iwandwip/TemperatureControlLab/sketch/py/data/test_Heaters.png

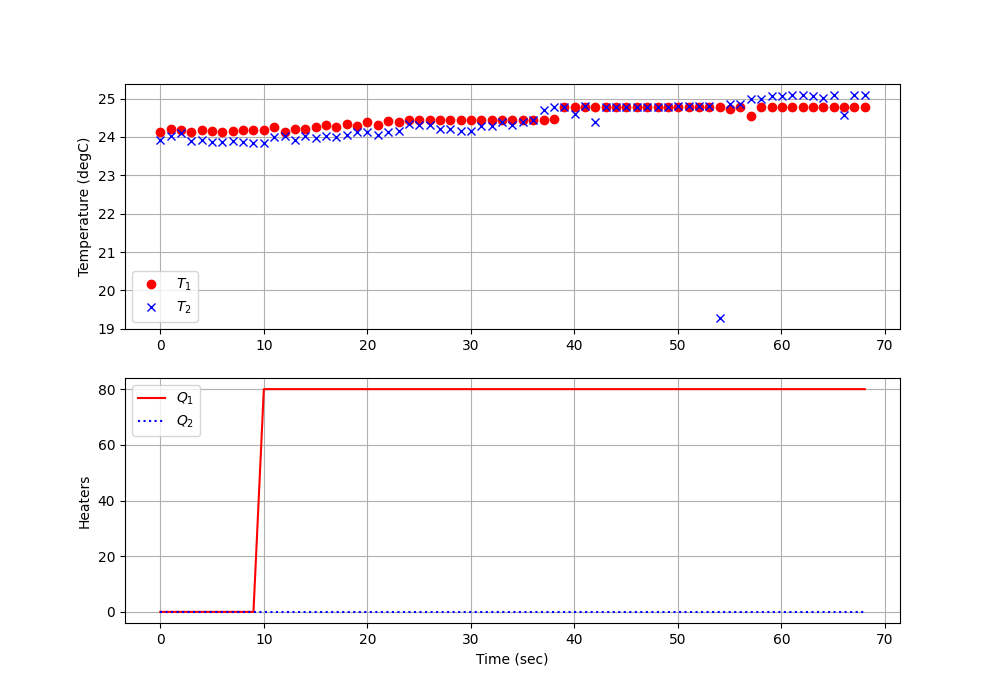
sketch/py/data/test_Heaters.png
