iwandwip/TemperatureControlLab/sketch/py/data/test_Models.png

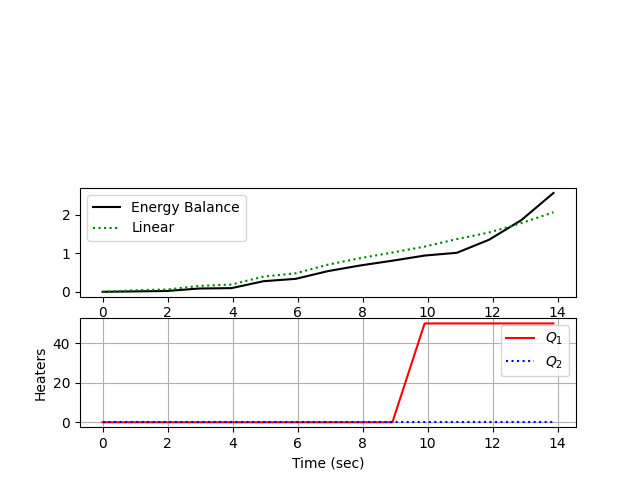
sketch/py/data/test_Models.png
