iwandwip/TemperatureControlLab/sketch/py/data/test_PID.png

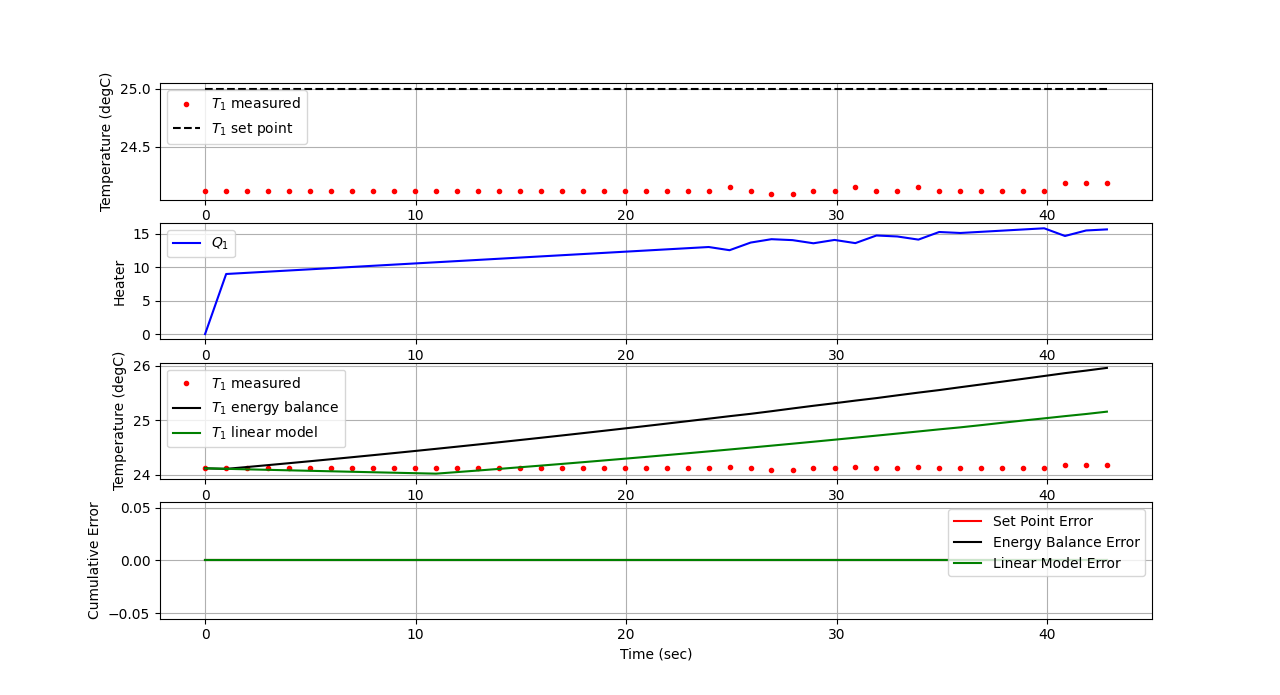
sketch/py/data/test_PID.png
